indyaceroni-png/GRRAASP/Supplemental Files/Supplemental FIles 1/sphere_2.stl

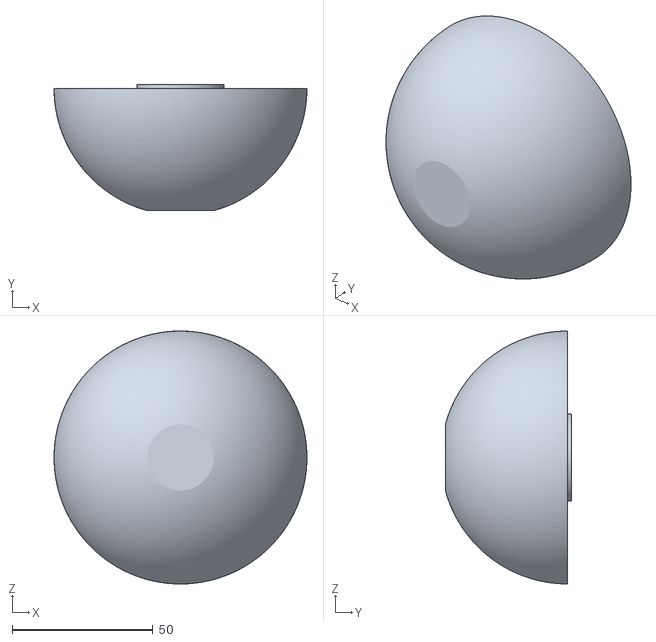
[picture p20: CAD file, 2026-07-03]
Supplemental Files/Supplemental FIles 1/sphere_2.stl
90.0 x 44.9 x 90.0
