indyaceroni-png/GRRAASP/Supplemental Files/Supplemental FIles 1/cylinder_1.stl

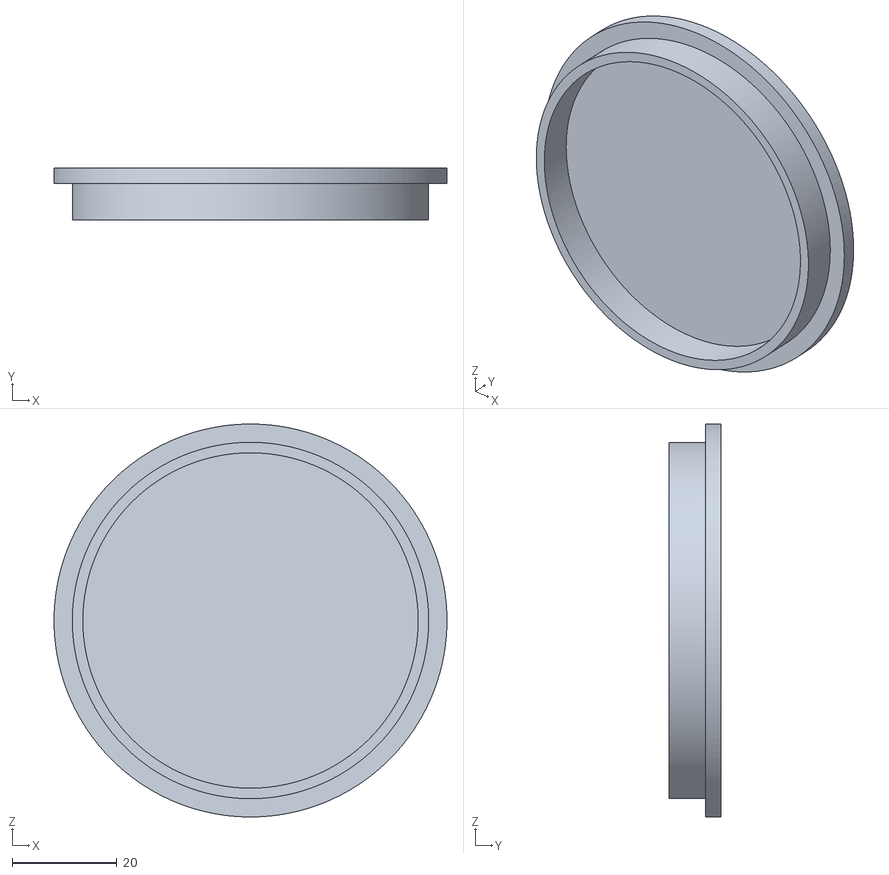
[picture p21: CAD file, 2026-07-03]
Supplemental Files/Supplemental FIles 1/cylinder_1.stl
75.0 x 10.0 x 75.0
