indyaceroni-png/GRRAASP/Supplemental Files/Supplemental FIles 2/5_platformTMount.stl

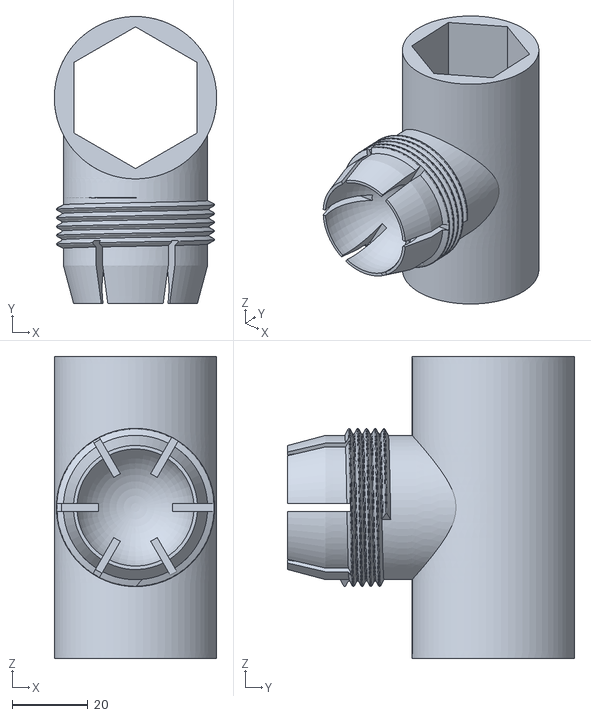
[picture p22: CAD file, 2026-07-03]
Supplemental Files/Supplemental FIles 2/5_platformTMount.stl
43.0 x 76.0 x 80.0
