indyaceroni-png/GRRAASP/Supplemental Files/Supplemental FIles 1/tridigital_2.stl

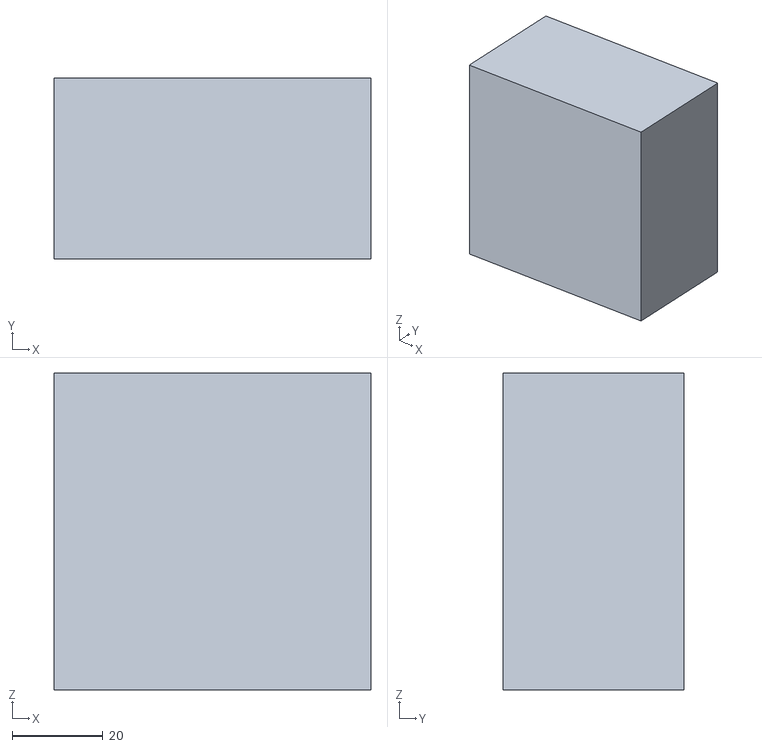
[picture p23: CAD file, 2026-07-03]
Supplemental Files/Supplemental FIles 1/tridigital_2.stl
70.0 x 40.0 x 70.0
